osamhack2020/IoT_KookMoBan_PonJohmNaimann/doc/iot_docu/circuit/circuit.jpg

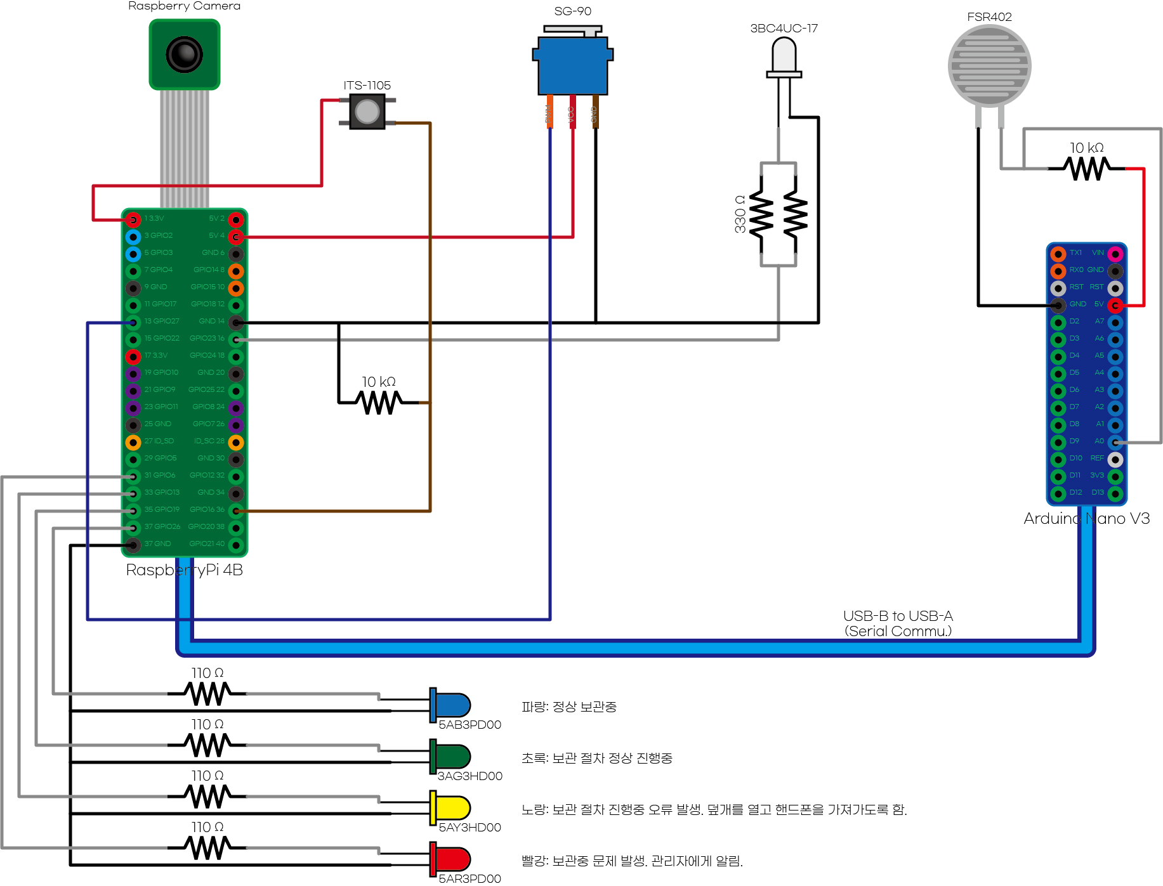
doc/iot_docu/circuit/circuit.jpg
