osamhack2020/IoT_KookMoBan_PonJohmNaimann/doc/iot_docu/hw_build_guide/02-1.jpg

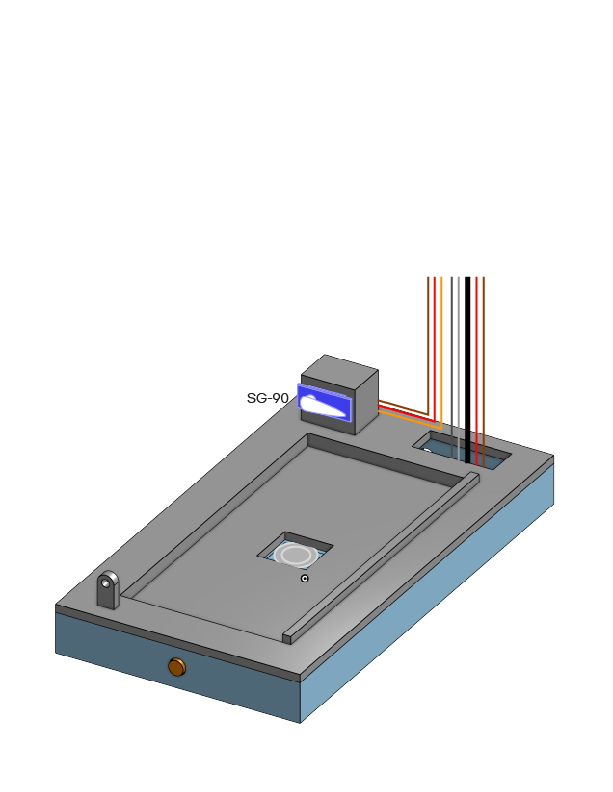
doc/iot_docu/hw_build_guide/02-1.jpg
